AvansETI/SmartMeter_DIY/Documentation/bouwhandleiding/1.png

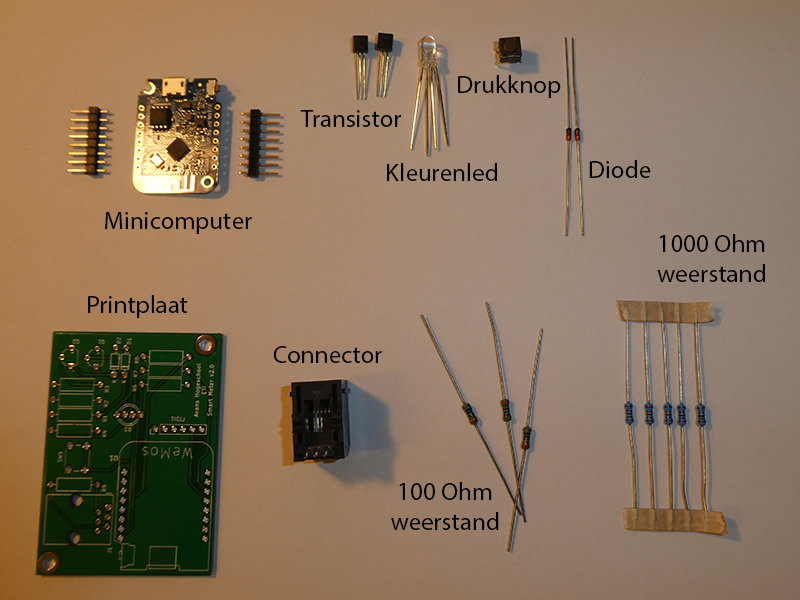
Documentation/bouwhandleiding/1.png
