AvansETI/SmartMeter_DIY/Documentation/bouwhandleiding/1a.png

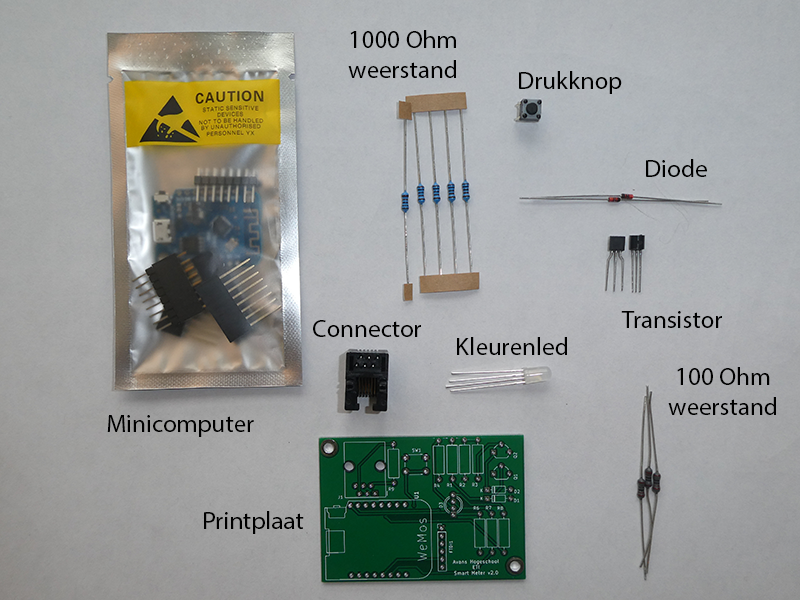
Documentation/bouwhandleiding/1a.png
