AvansETI/SmartMeter_DIY/Documentation/bouwhandleiding/2.png

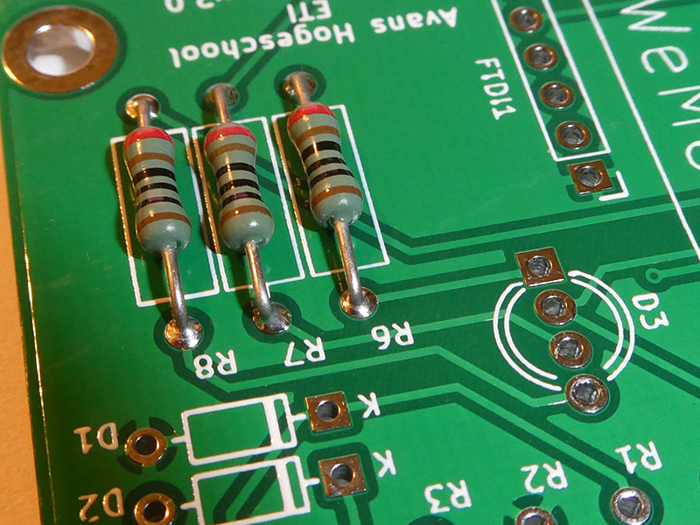
Documentation/bouwhandleiding/2.png
