AvansETI/SmartMeter_DIY/Documentation/bouwhandleiding/3.png

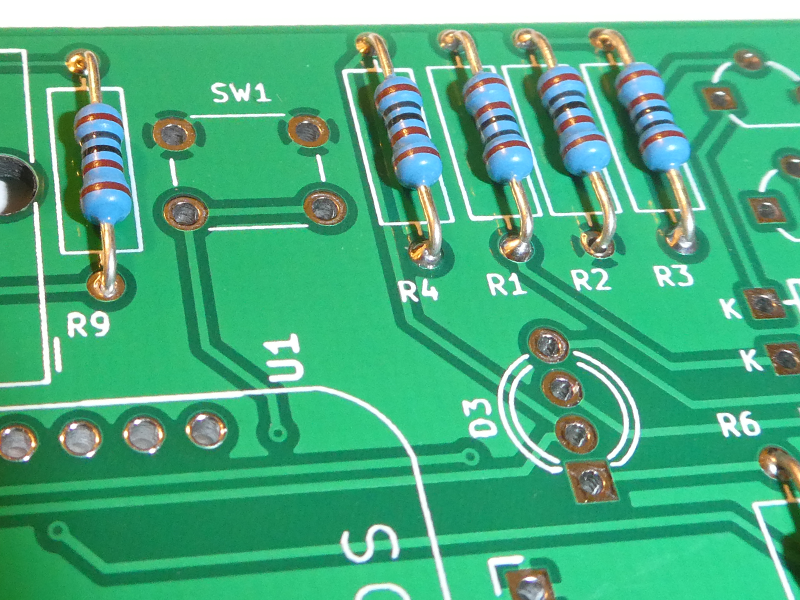
Documentation/bouwhandleiding/3.png
