AvansETI/SmartMeter_DIY/Documentation/bouwhandleiding/4.png

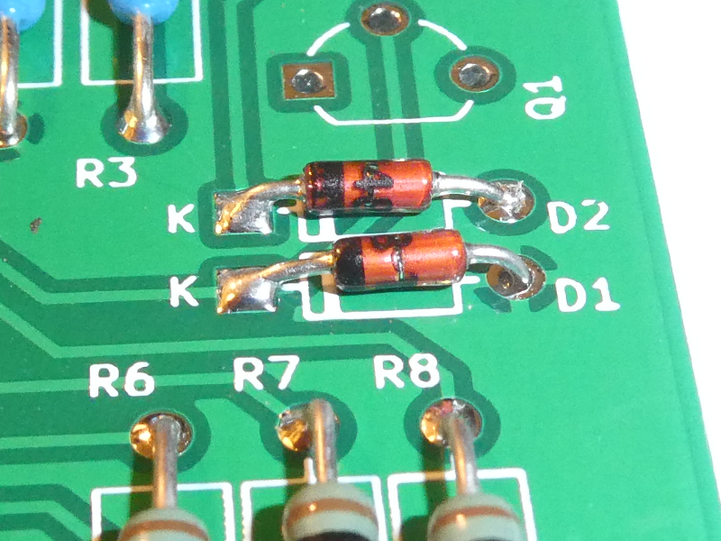
Documentation/bouwhandleiding/4.png
