AvansETI/SmartMeter_DIY/Documentation/bouwhandleiding/5.png

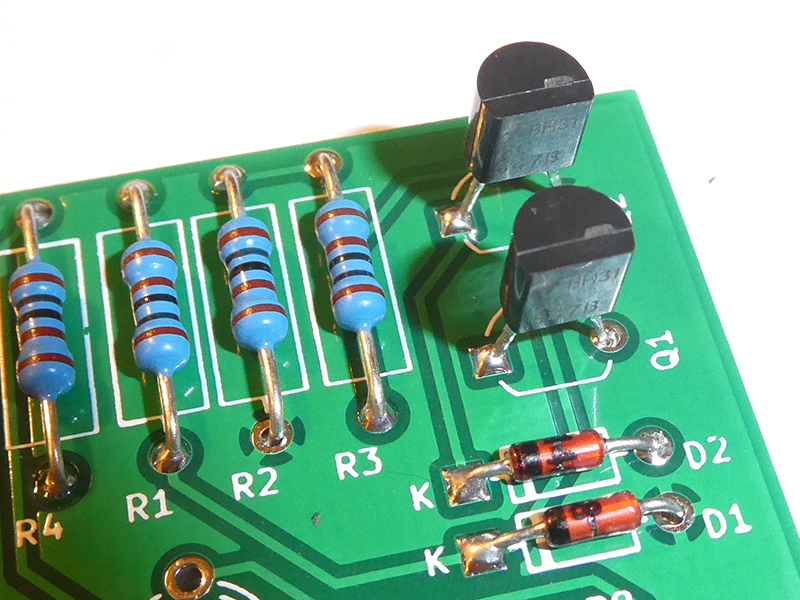
Documentation/bouwhandleiding/5.png
