AvansETI/SmartMeter_DIY/Documentation/bouwhandleiding/6.png

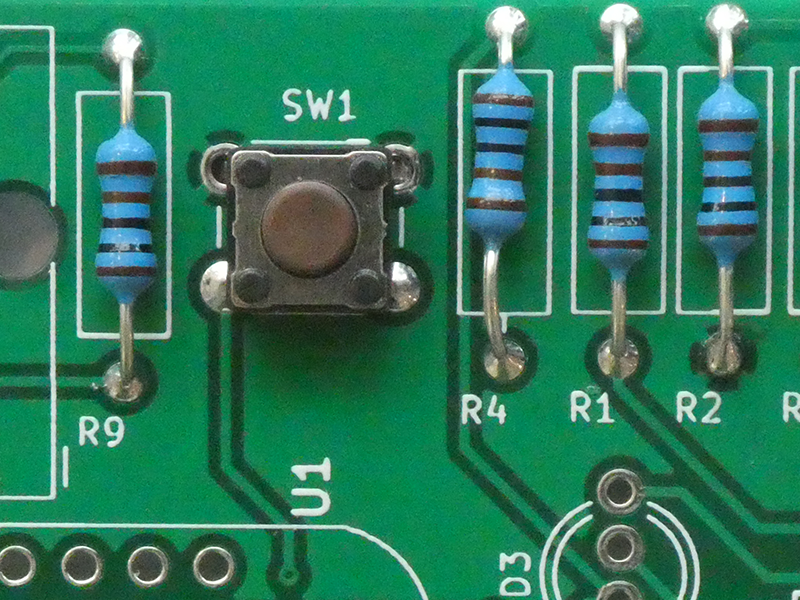
Documentation/bouwhandleiding/6.png
