AvansETI/SmartMeter_DIY/Documentation/bouwhandleiding/7.png

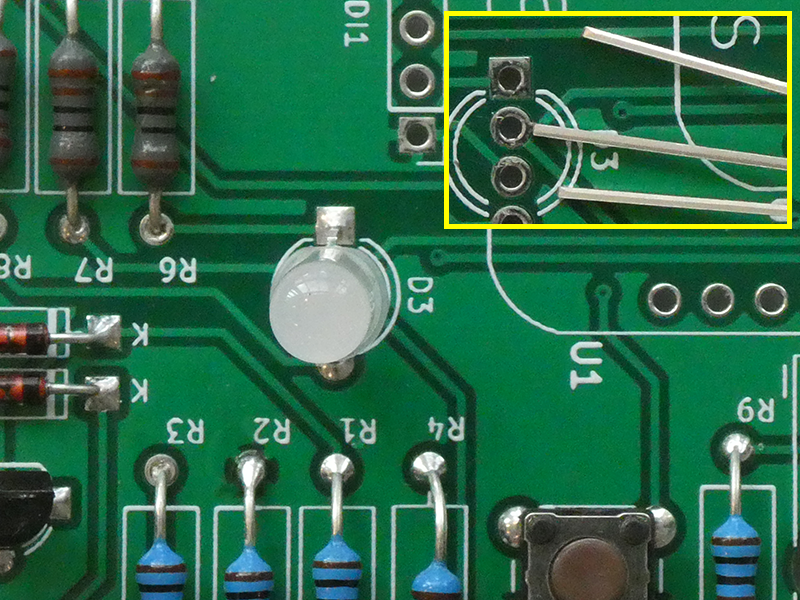
Documentation/bouwhandleiding/7.png
