AvansETI/SmartMeter_DIY/Documentation/bouwhandleiding/8.png

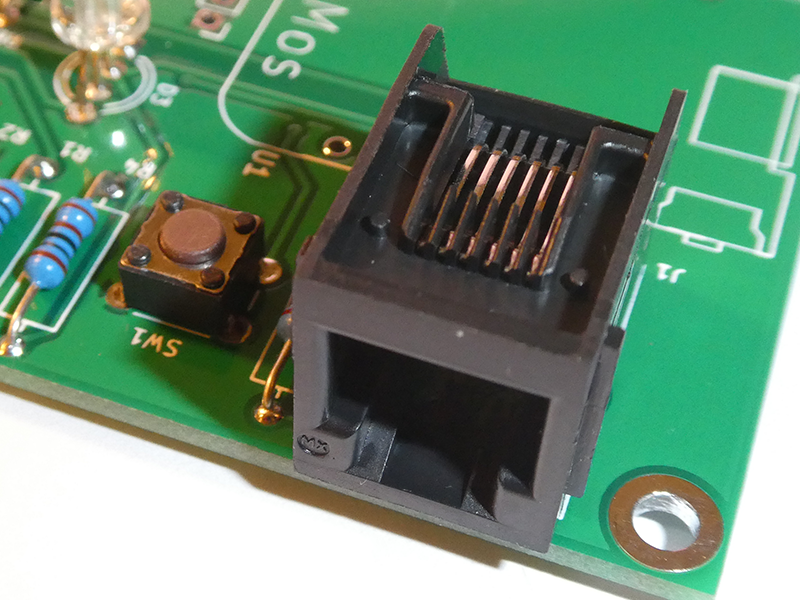
Documentation/bouwhandleiding/8.png
