AvansETI/SmartMeter_DIY/Documentation/bouwhandleiding/9.png

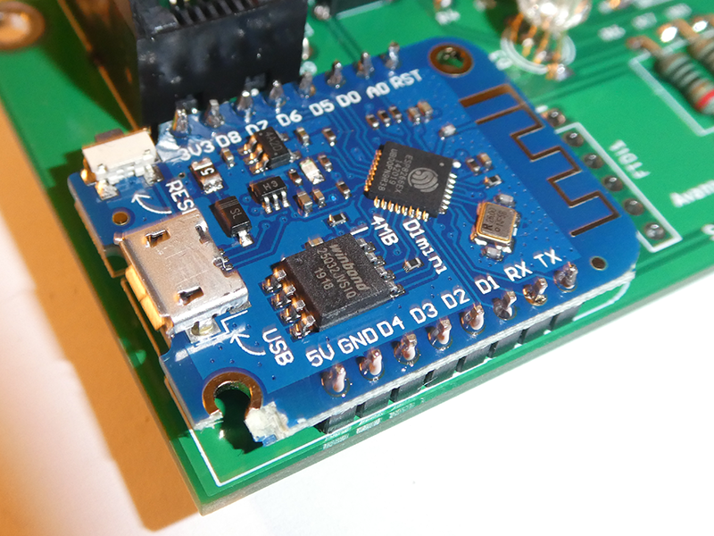
Documentation/bouwhandleiding/9.png
