AvansETI/SmartMeter_DIY/Documentation/bouwhandleiding/9a.png

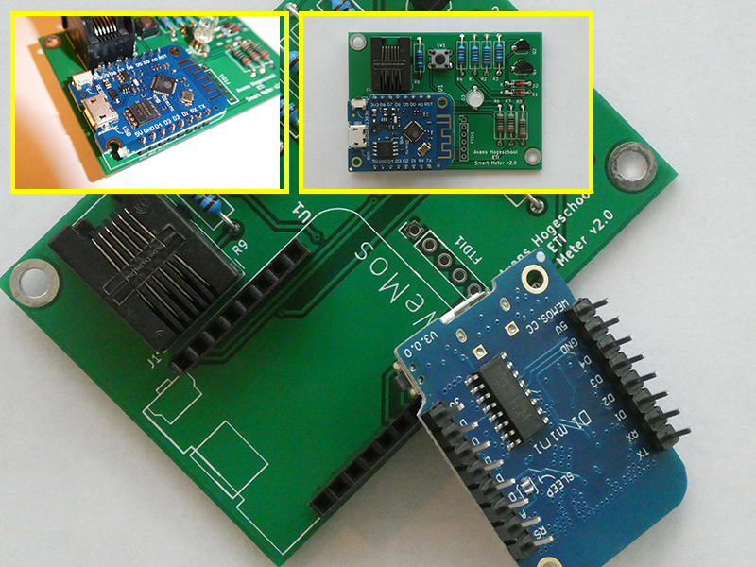
Documentation/bouwhandleiding/9a.png
