AvansETI/SmartMeter_DIY/Documentation/bouwhandleiding/handleiding.png

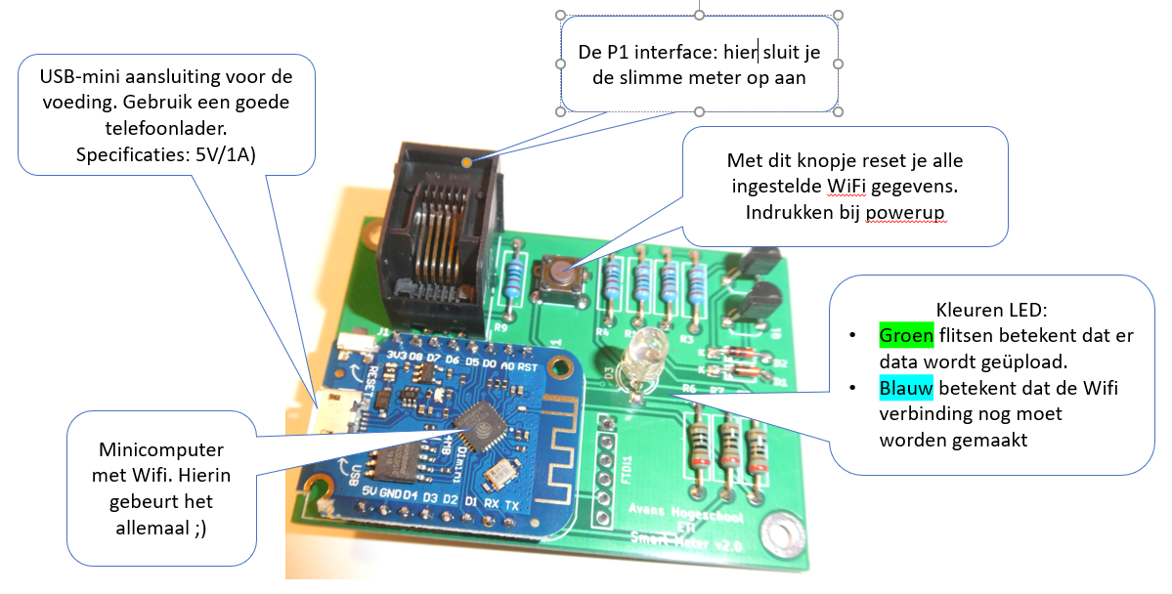
Documentation/bouwhandleiding/handleiding.png
