AvansETI/SmartMeter_DIY/Documentation/bouwhandleiding/smartmeter-5.gif

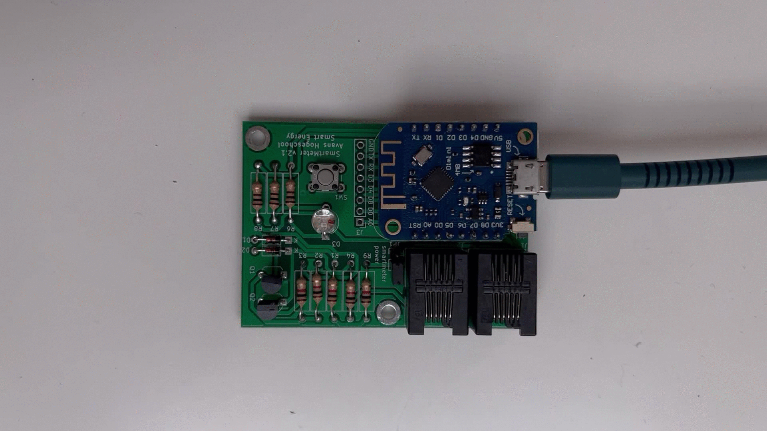
Documentation/bouwhandleiding/smartmeter-5.gif
