AvansETI/SmartMeter_DIY/Documentation/bouwhandleiding/smartmeter-05.gif

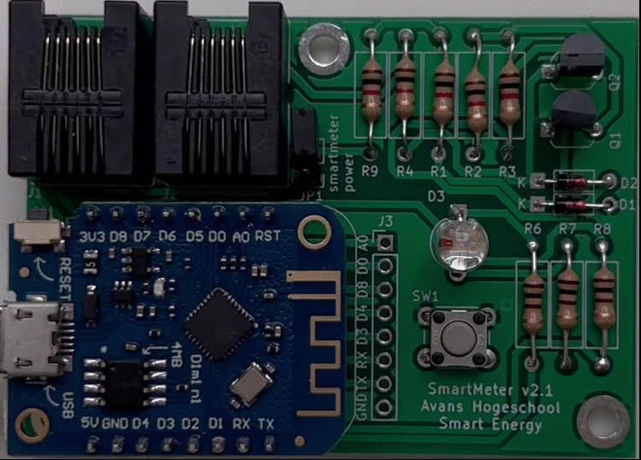
Documentation/bouwhandleiding/smartmeter-05.gif
