AvansETI/SmartMeter_DIY/Documentation/bouwhandleiding/stap_01.png

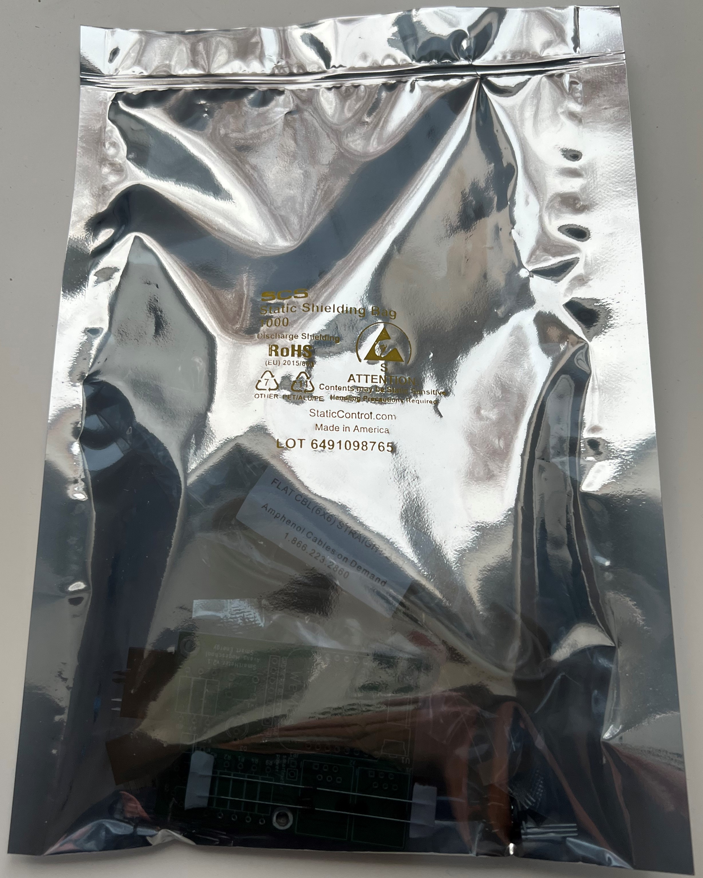
Documentation/bouwhandleiding/stap_01.png
