AvansETI/SmartMeter_DIY/Documentation/bouwhandleiding/stap_02.png

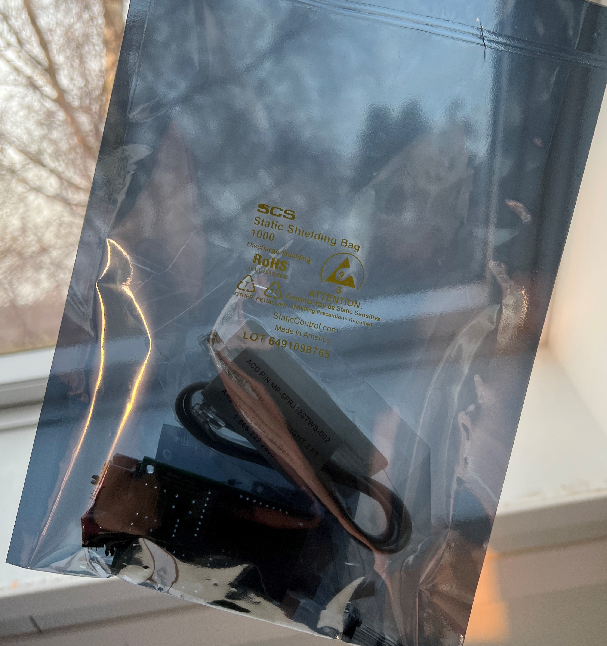
Documentation/bouwhandleiding/stap_02.png
