AvansETI/SmartMeter_DIY/Documentation/bouwhandleiding/stap_03.png

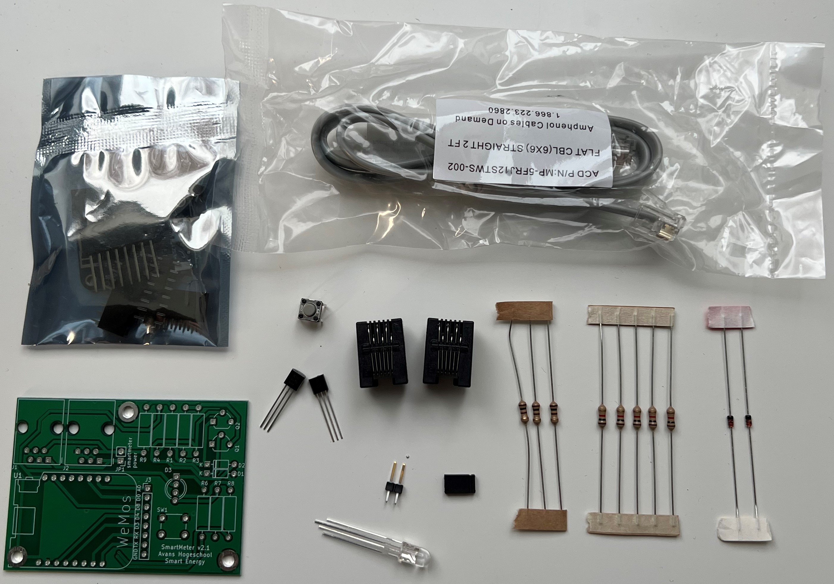
Documentation/bouwhandleiding/stap_03.png
