AvansETI/SmartMeter_DIY/Documentation/bouwhandleiding/stap_04.png

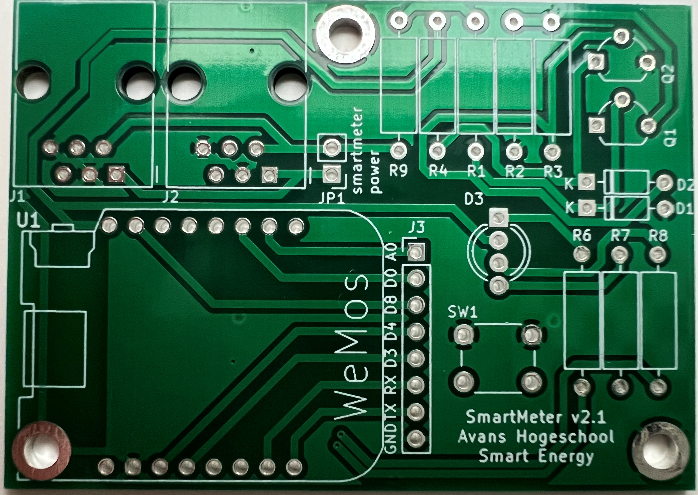
Documentation/bouwhandleiding/stap_04.png
