AvansETI/SmartMeter_DIY/Documentation/bouwhandleiding/stap_05.png

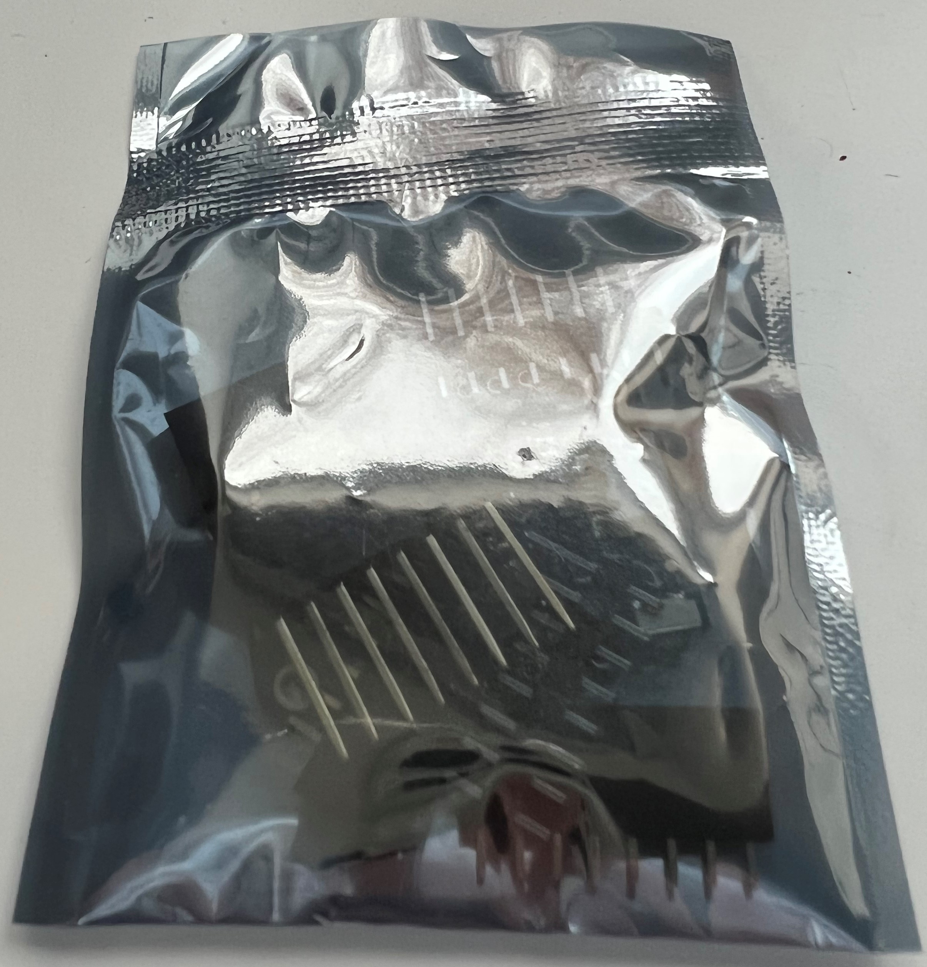
Documentation/bouwhandleiding/stap_05.png
