AvansETI/SmartMeter_DIY/Documentation/bouwhandleiding/stap_06.png

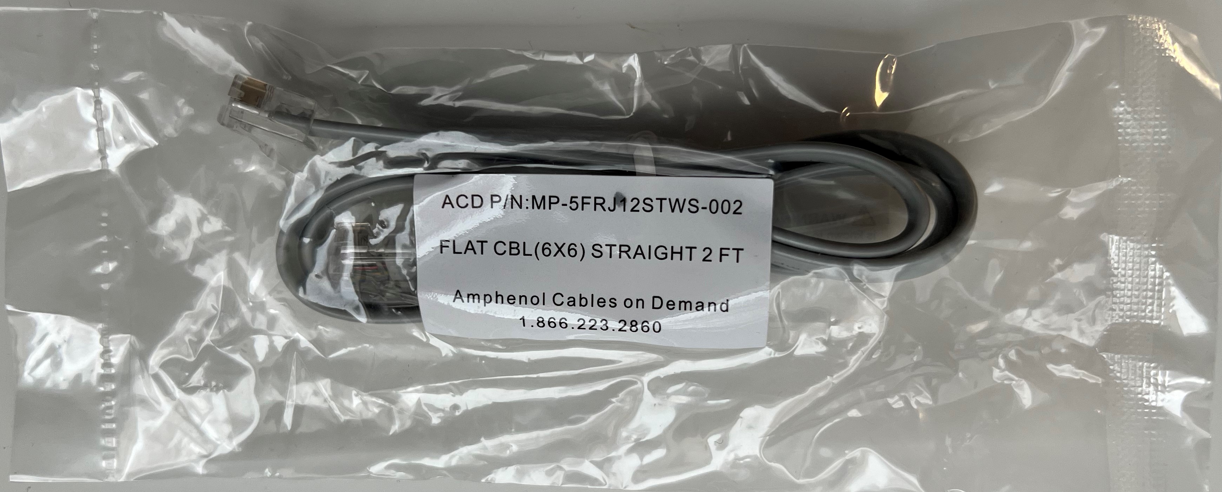
Documentation/bouwhandleiding/stap_06.png
