AvansETI/SmartMeter_DIY/Documentation/bouwhandleiding/stap_07.png

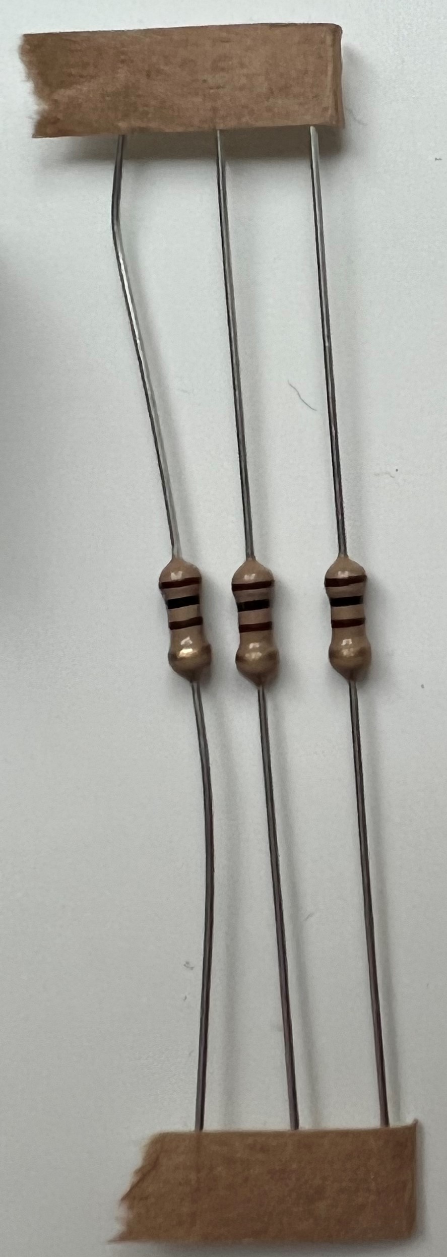
Documentation/bouwhandleiding/stap_07.png
