AvansETI/SmartMeter_DIY/Documentation/bouwhandleiding/stap_08.png

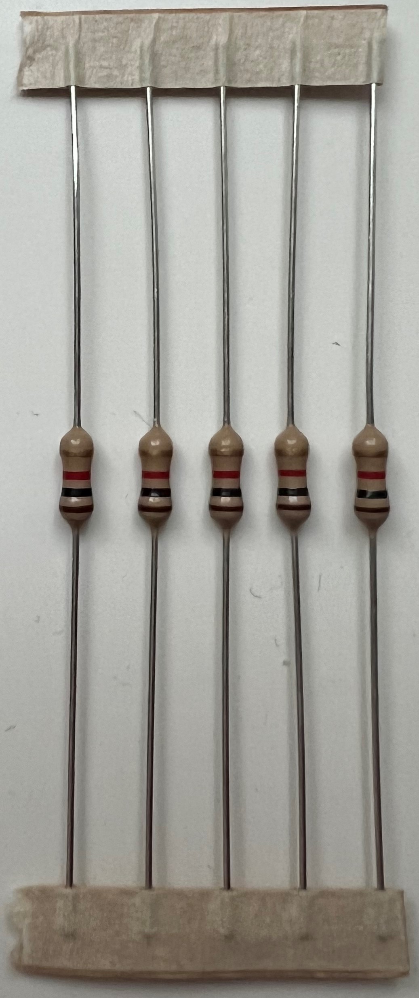
Documentation/bouwhandleiding/stap_08.png
