AvansETI/SmartMeter_DIY/Documentation/bouwhandleiding/stap_09.png

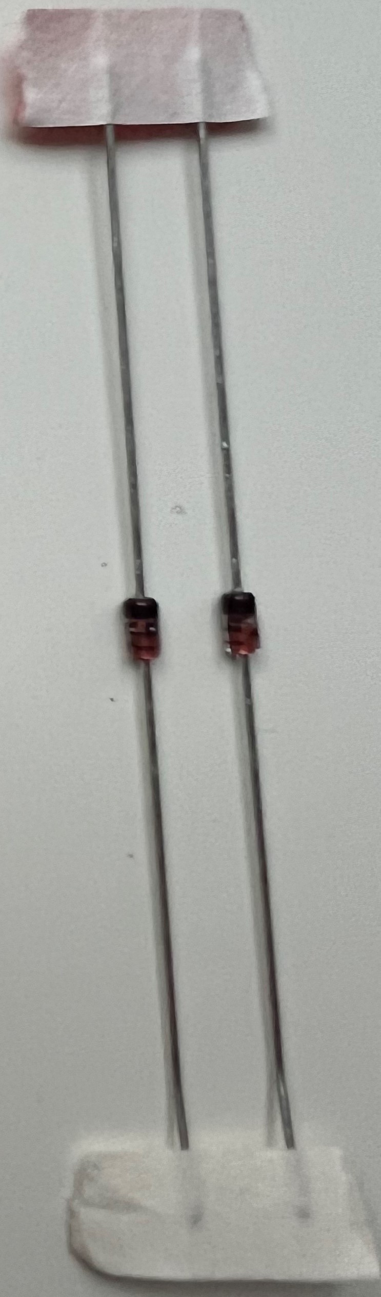
Documentation/bouwhandleiding/stap_09.png
