AvansETI/SmartMeter_DIY/Documentation/bouwhandleiding/stap_10.png

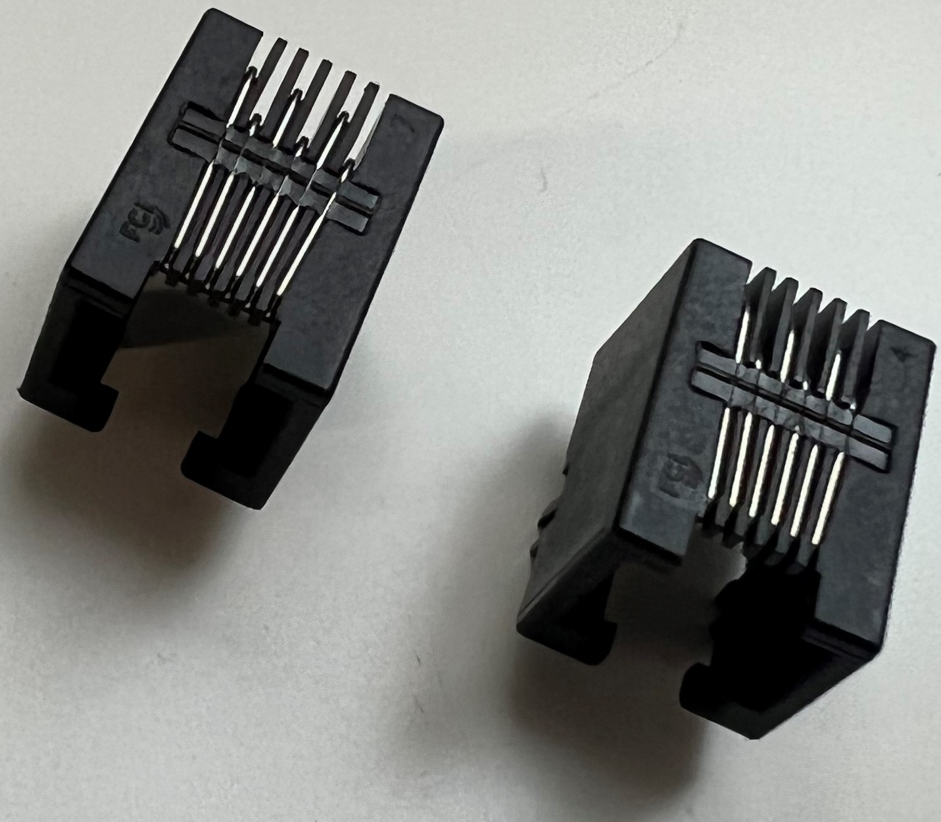
Documentation/bouwhandleiding/stap_10.png
