AvansETI/SmartMeter_DIY/Documentation/bouwhandleiding/stap_11.png

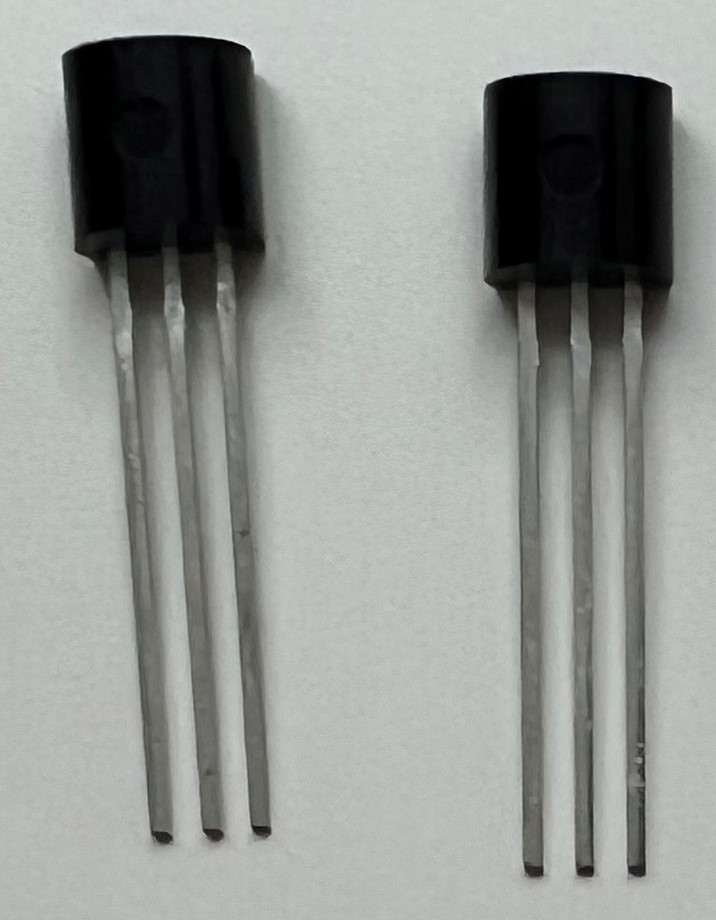
Documentation/bouwhandleiding/stap_11.png
