AvansETI/SmartMeter_DIY/Documentation/bouwhandleiding/stap_13.png

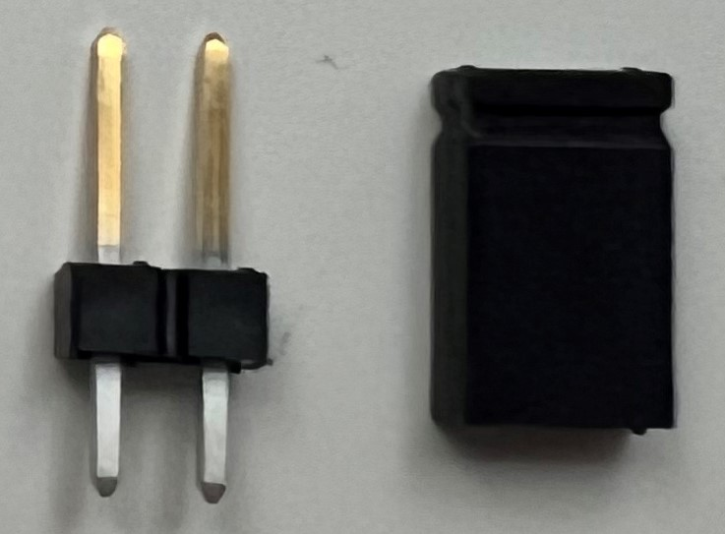
Documentation/bouwhandleiding/stap_13.png
