AvansETI/SmartMeter_DIY/Documentation/bouwhandleiding/stap_15.png

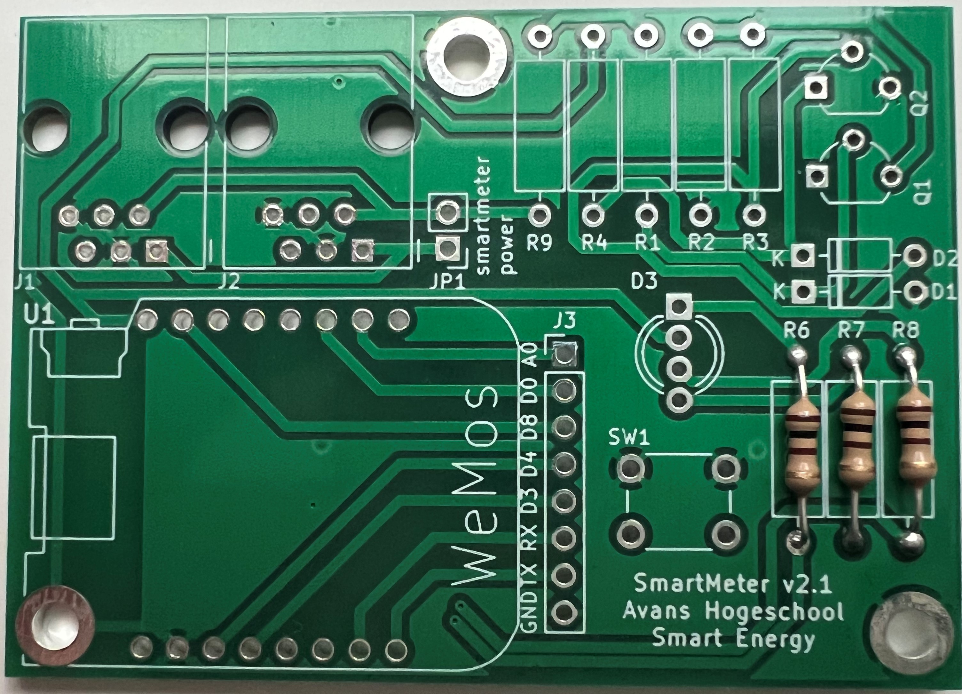
Documentation/bouwhandleiding/stap_15.png
