AvansETI/SmartMeter_DIY/Documentation/bouwhandleiding/stap_17.png

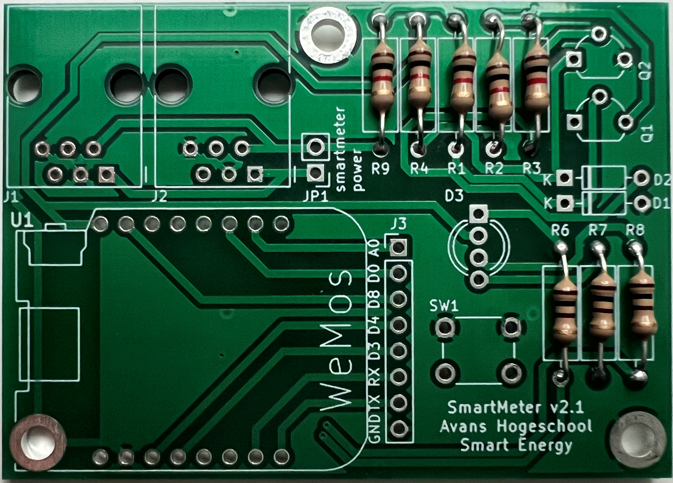
Documentation/bouwhandleiding/stap_17.png
