AvansETI/SmartMeter_DIY/Documentation/bouwhandleiding/stap_19.png

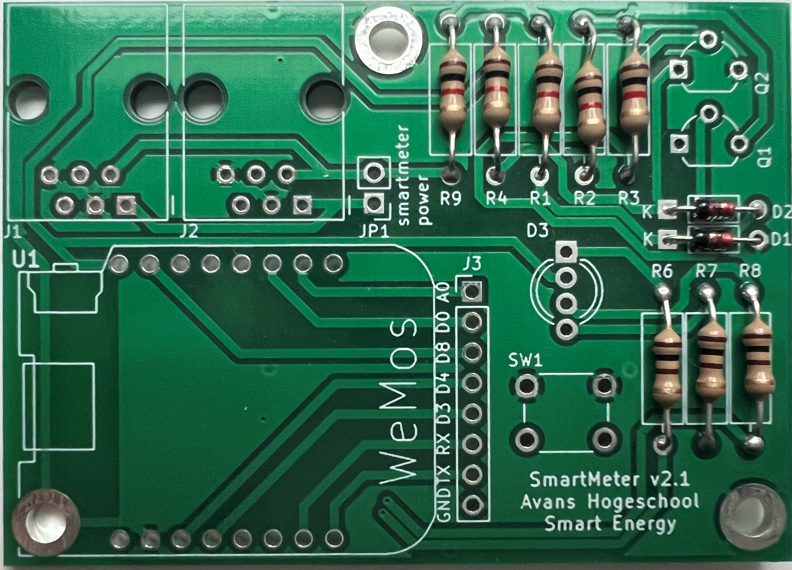
Documentation/bouwhandleiding/stap_19.png
