AvansETI/SmartMeter_DIY/Documentation/bouwhandleiding/stap_21.png

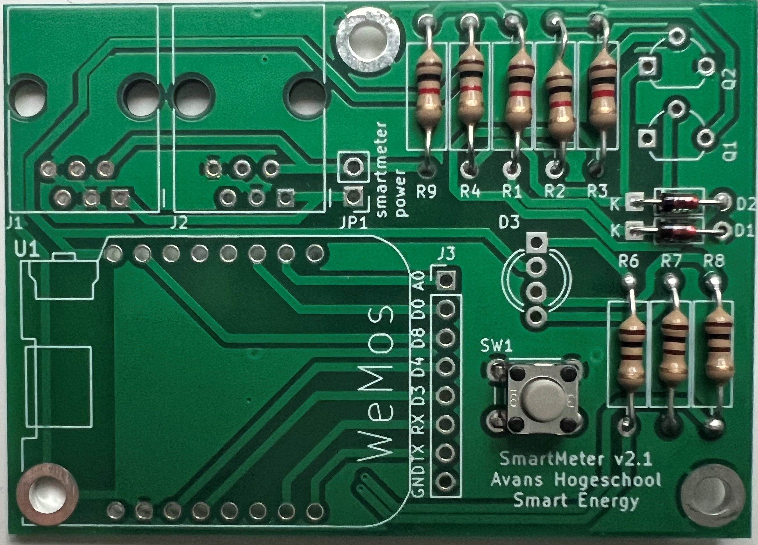
Documentation/bouwhandleiding/stap_21.png
