AvansETI/SmartMeter_DIY/Documentation/bouwhandleiding/stap_23.png

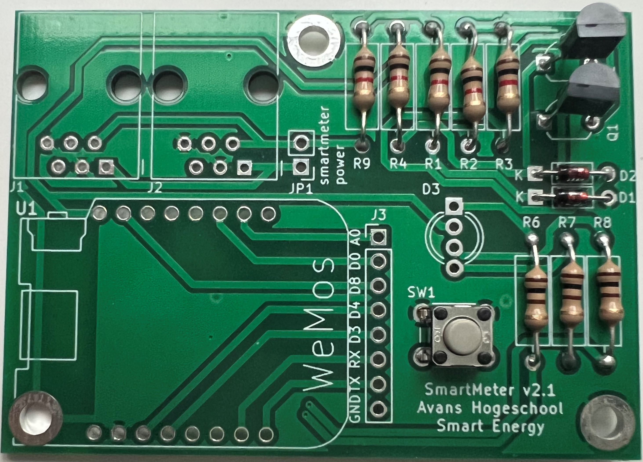
Documentation/bouwhandleiding/stap_23.png
