AvansETI/SmartMeter_DIY/Documentation/bouwhandleiding/stap_25.png

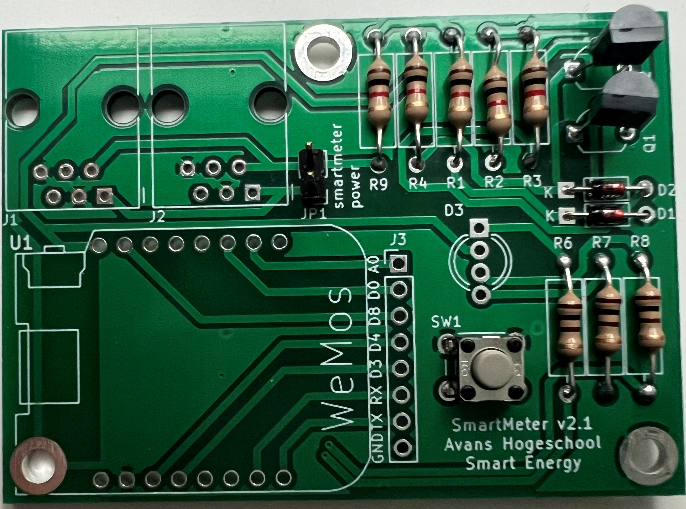
Documentation/bouwhandleiding/stap_25.png
