AvansETI/SmartMeter_DIY/Documentation/bouwhandleiding/stap_27.png

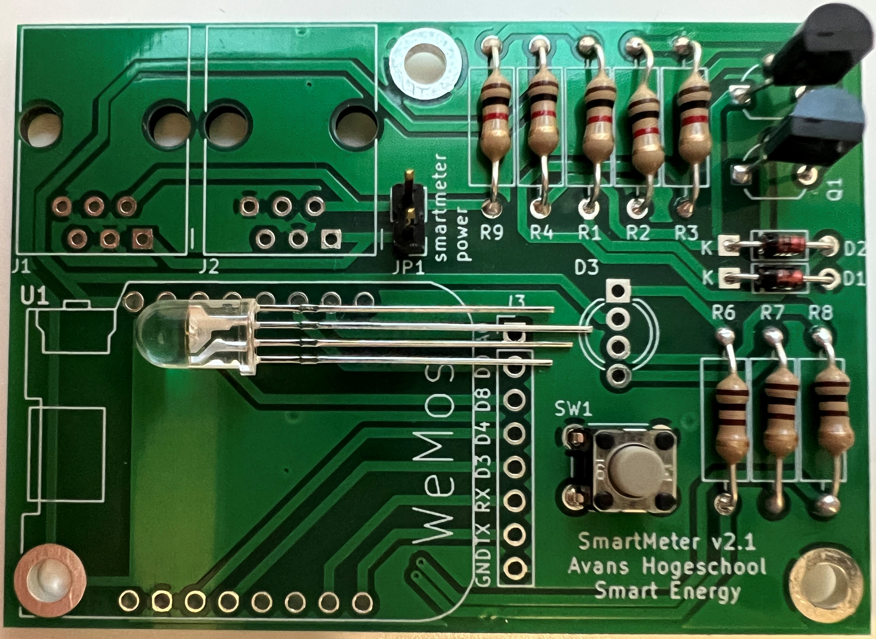
Documentation/bouwhandleiding/stap_27.png
