AvansETI/SmartMeter_DIY/Documentation/bouwhandleiding/stap_29.png

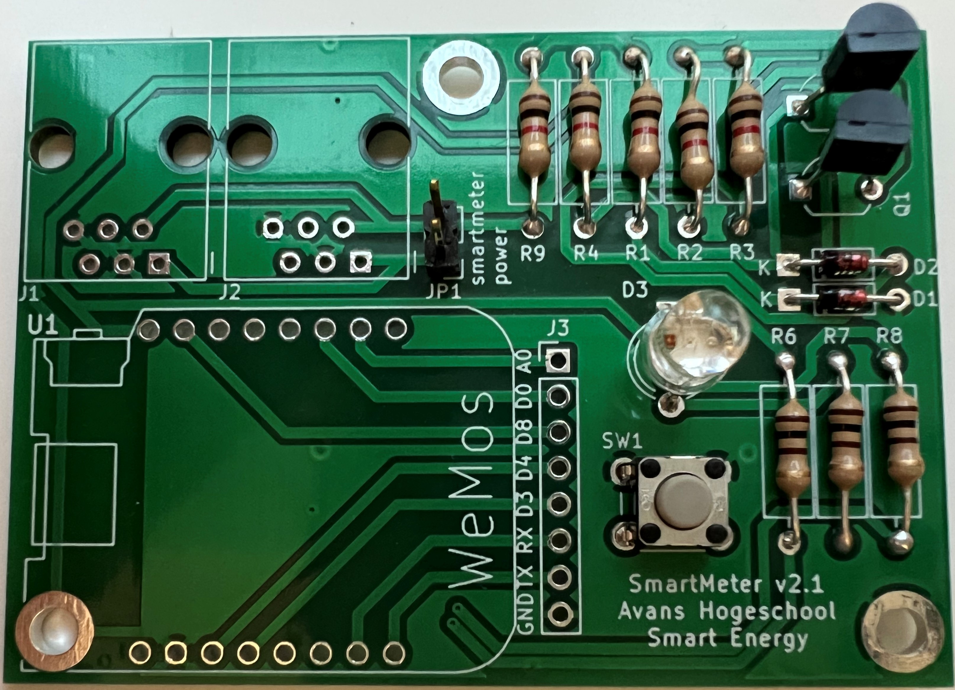
Documentation/bouwhandleiding/stap_29.png
