AvansETI/SmartMeter_DIY/Documentation/bouwhandleiding/stap_32.png

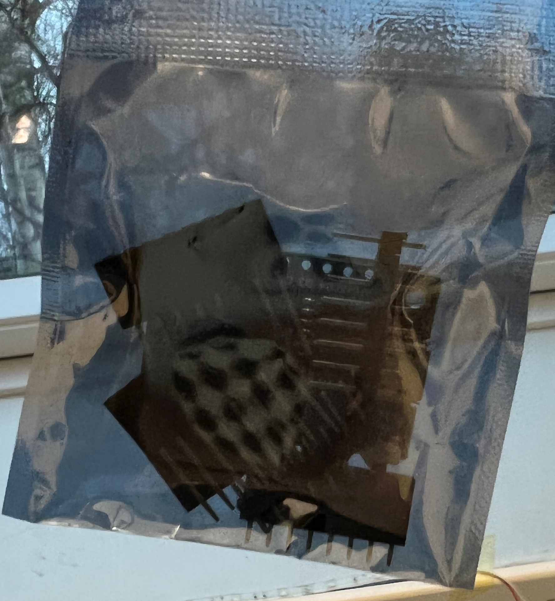
Documentation/bouwhandleiding/stap_32.png
