AvansETI/SmartMeter_DIY/Documentation/bouwhandleiding/stap_37.png

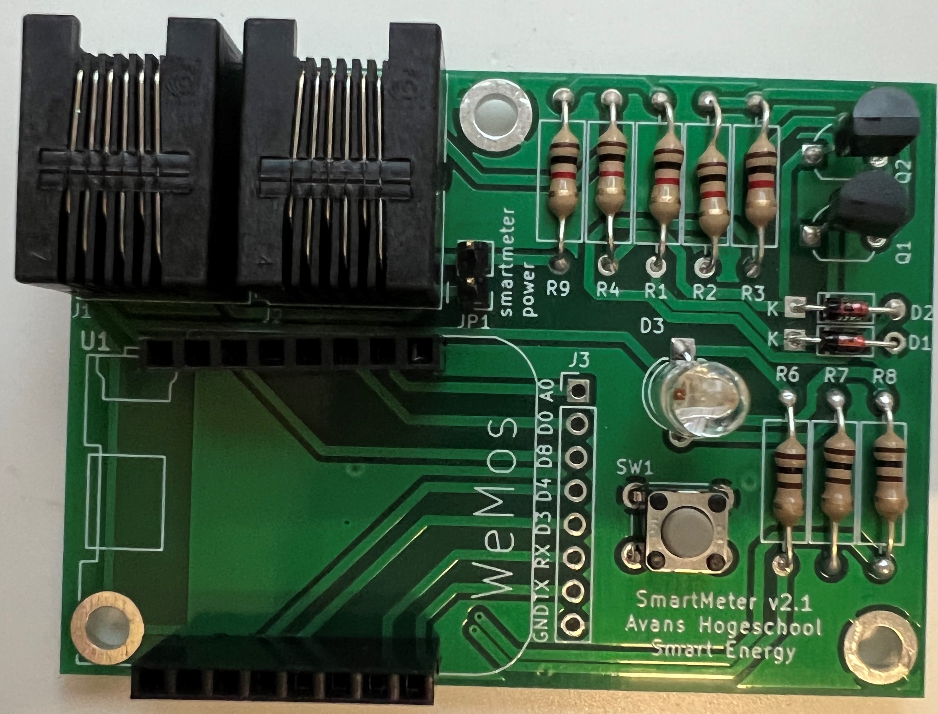
Documentation/bouwhandleiding/stap_37.png
