AvansETI/SmartMeter_DIY/Documentation/bouwhandleiding/stap_40.png

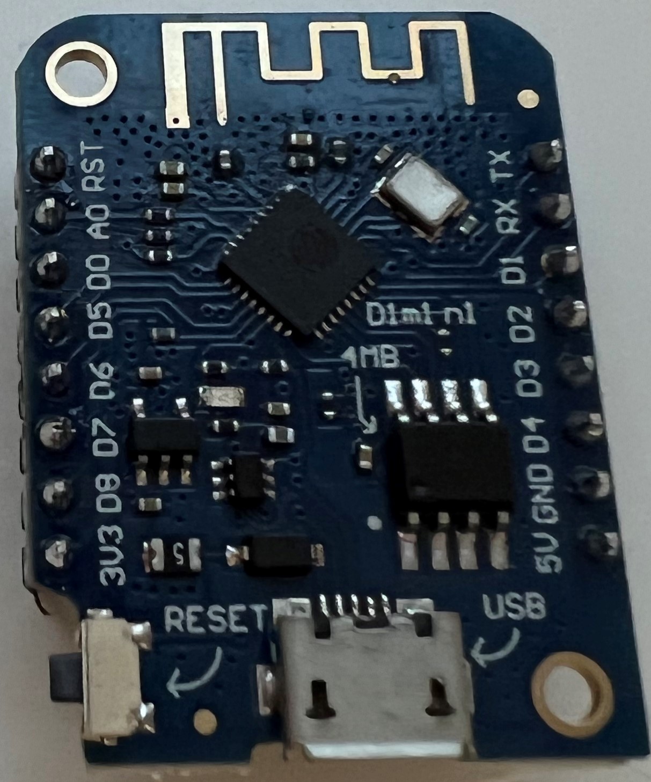
Documentation/bouwhandleiding/stap_40.png
