AvansETI/SmartMeter_DIY/Documentation/bouwhandleiding/stap_41.png

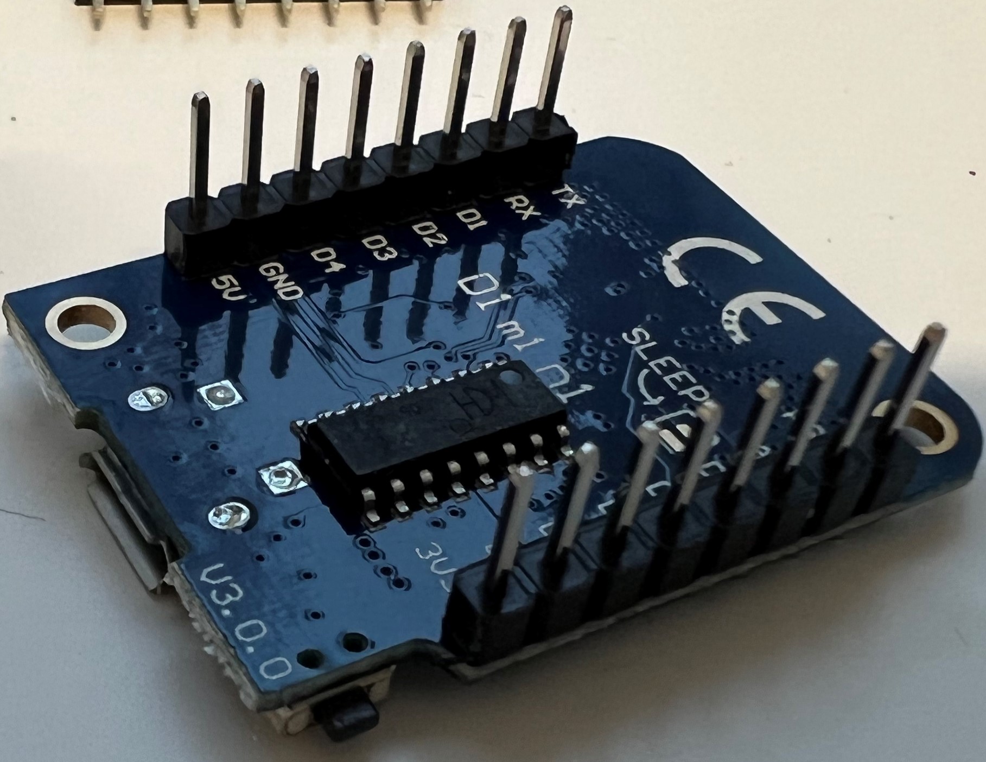
Documentation/bouwhandleiding/stap_41.png
