AvansETI/SmartMeter_DIY/Documentation/bouwhandleiding/stap_42.png

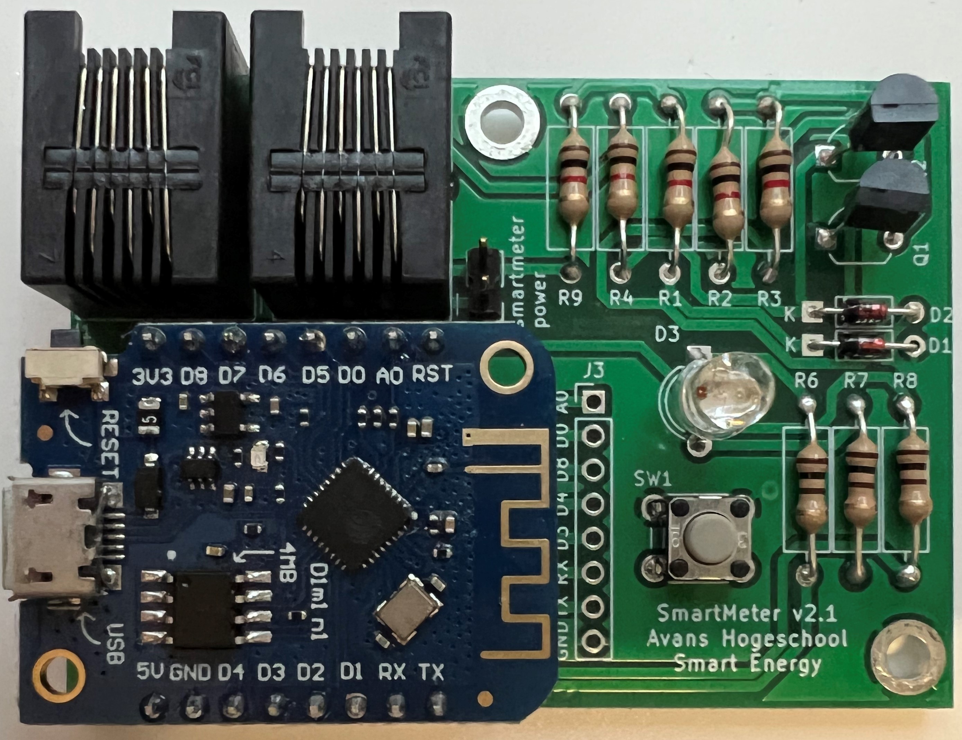
Documentation/bouwhandleiding/stap_42.png
