AvansETI/SmartMeter_DIY/Documentation/bouwhandleiding/stap_44.png

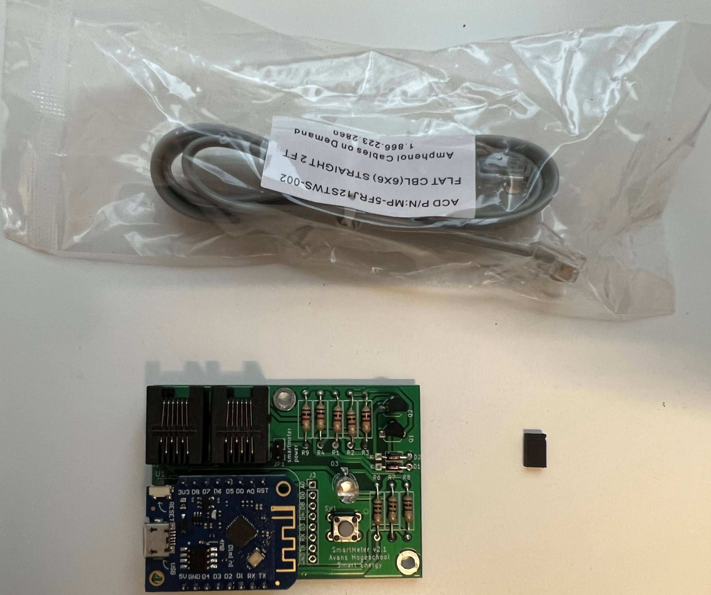
Documentation/bouwhandleiding/stap_44.png
