AvansETI/SmartMeter_DIY/Documentation/bouwhandleiding/stap_45.png

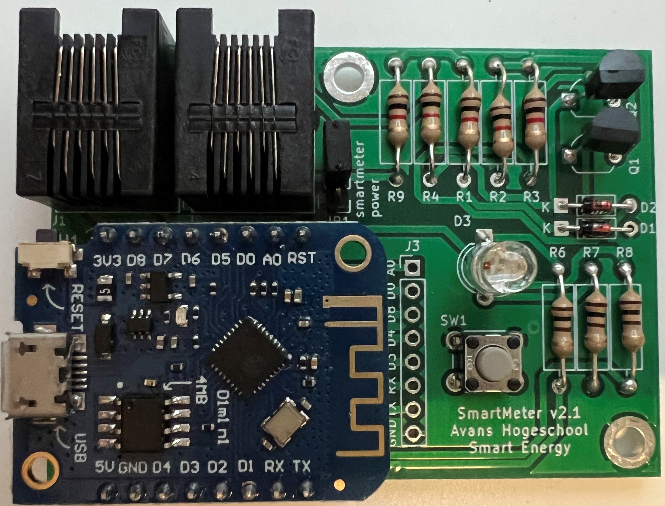
Documentation/bouwhandleiding/stap_45.png
