AvansETI/SmartMeter_DIY/Documentation/bouwhandleiding/stap_49.png

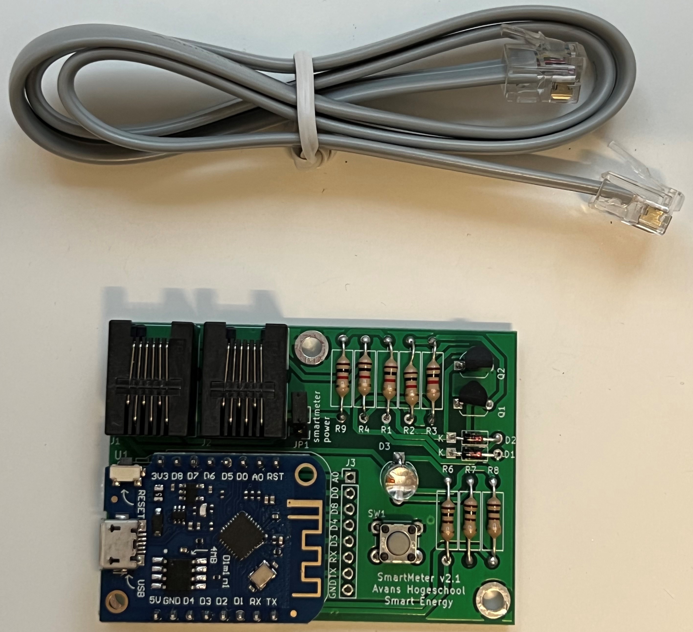
Documentation/bouwhandleiding/stap_49.png
