AvansETI/SmartMeter_DIY/Documentation/bouwhandleiding/stap_50.png

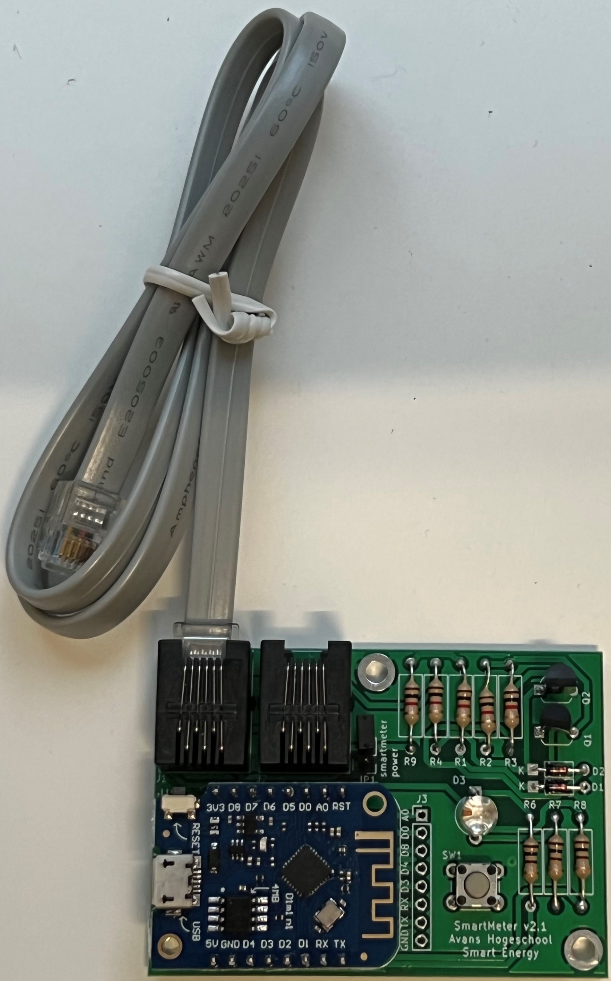
Documentation/bouwhandleiding/stap_50.png
