AvansETI/SmartMeter_DIY/Documentation/bouwhandleiding/wifi-1.png

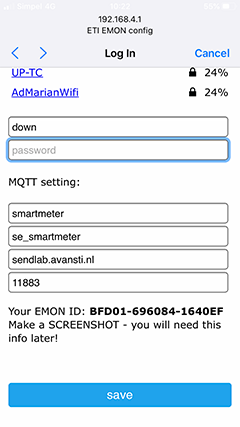
Documentation/bouwhandleiding/wifi-1.png
